freetronics/POEREG/Images/100_1713.JPG

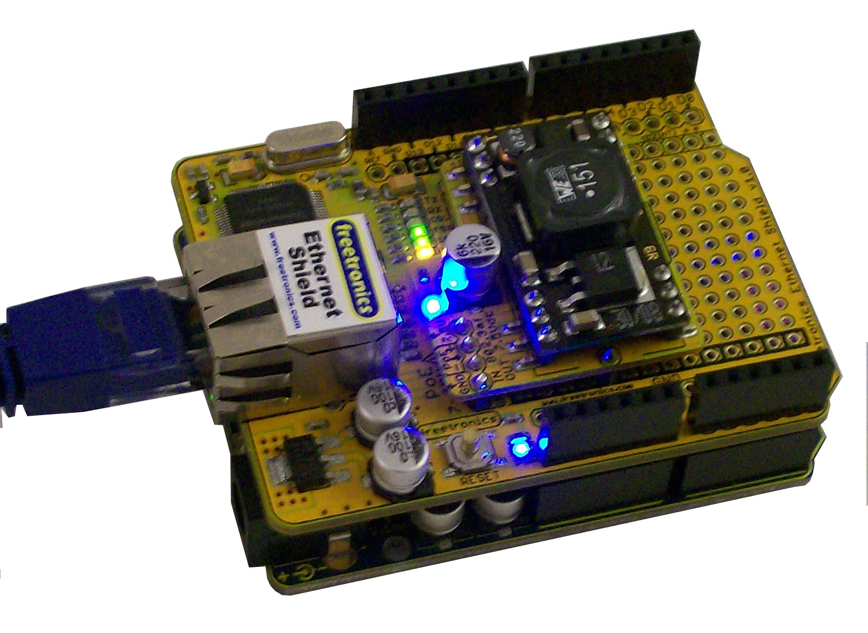
Images/100_1713.JPG
