freetronics/POEREG/Images/100_1719.JPG

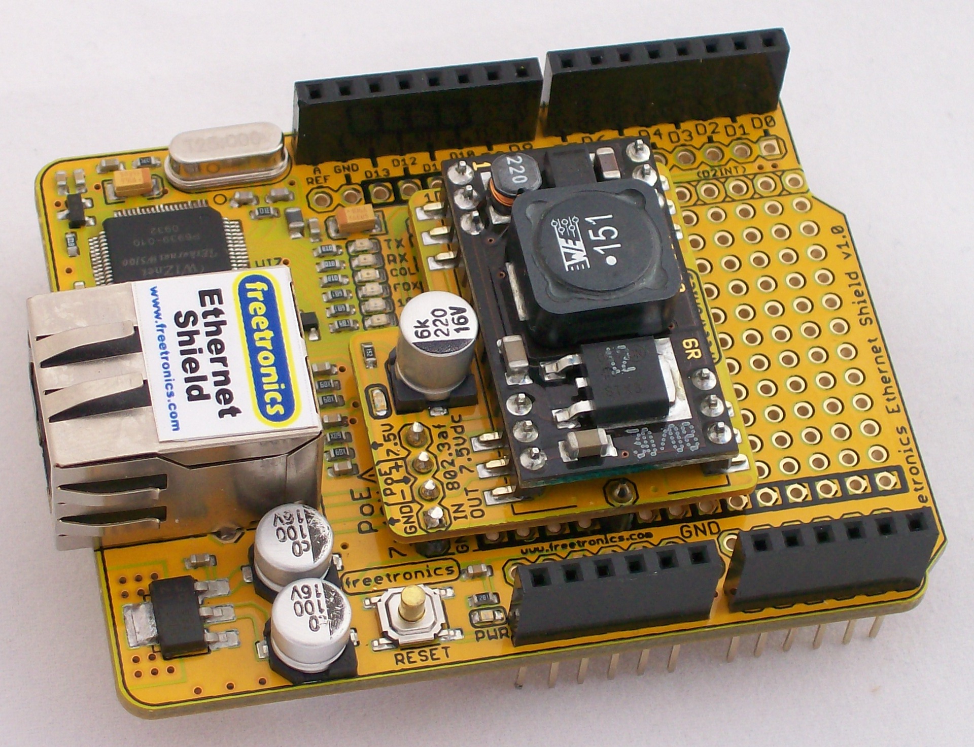
Images/100_1719.JPG
