freetronics/POEREG/Images/DSCF0289.JPG

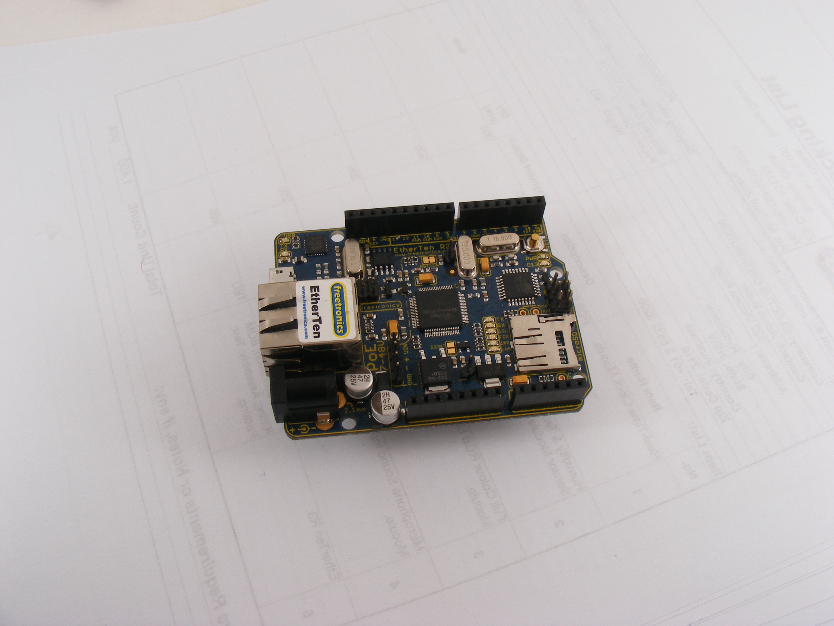
Images/DSCF0289.JPG
