freetronics/POEREG/Images/DSCF0290.JPG

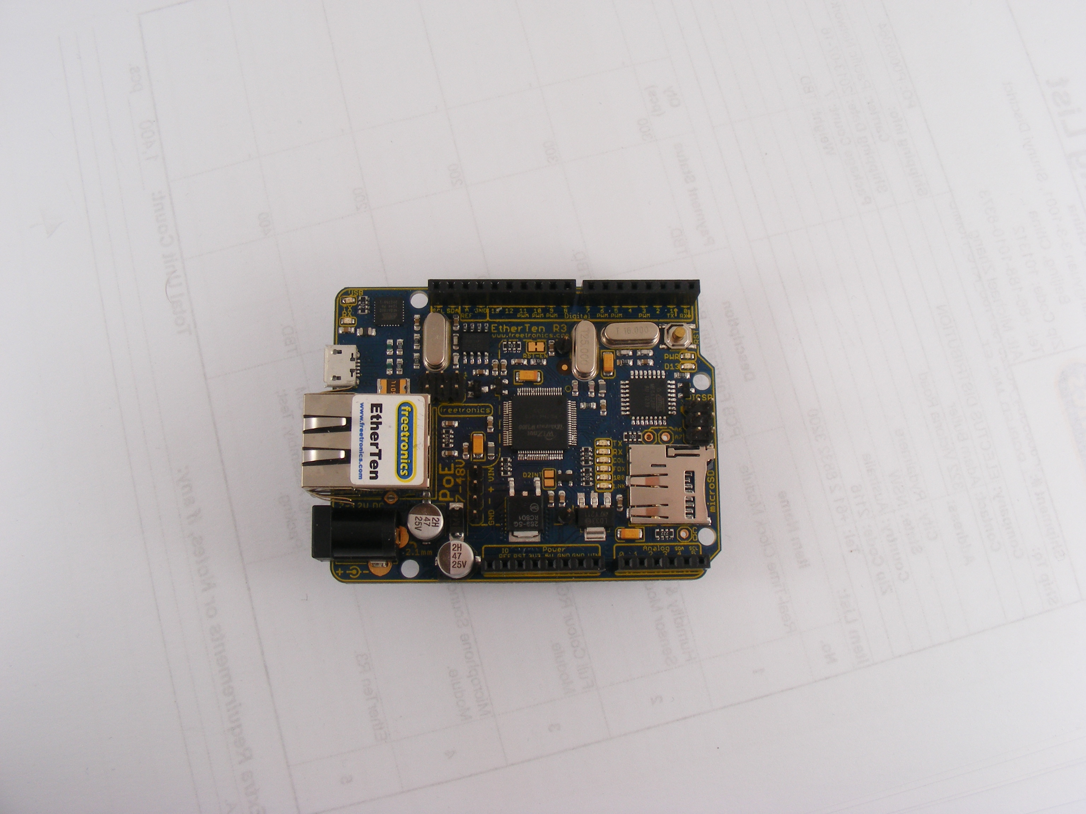
Images/DSCF0290.JPG
