freetronics/POEREG/Images/DSCF0296.JPG

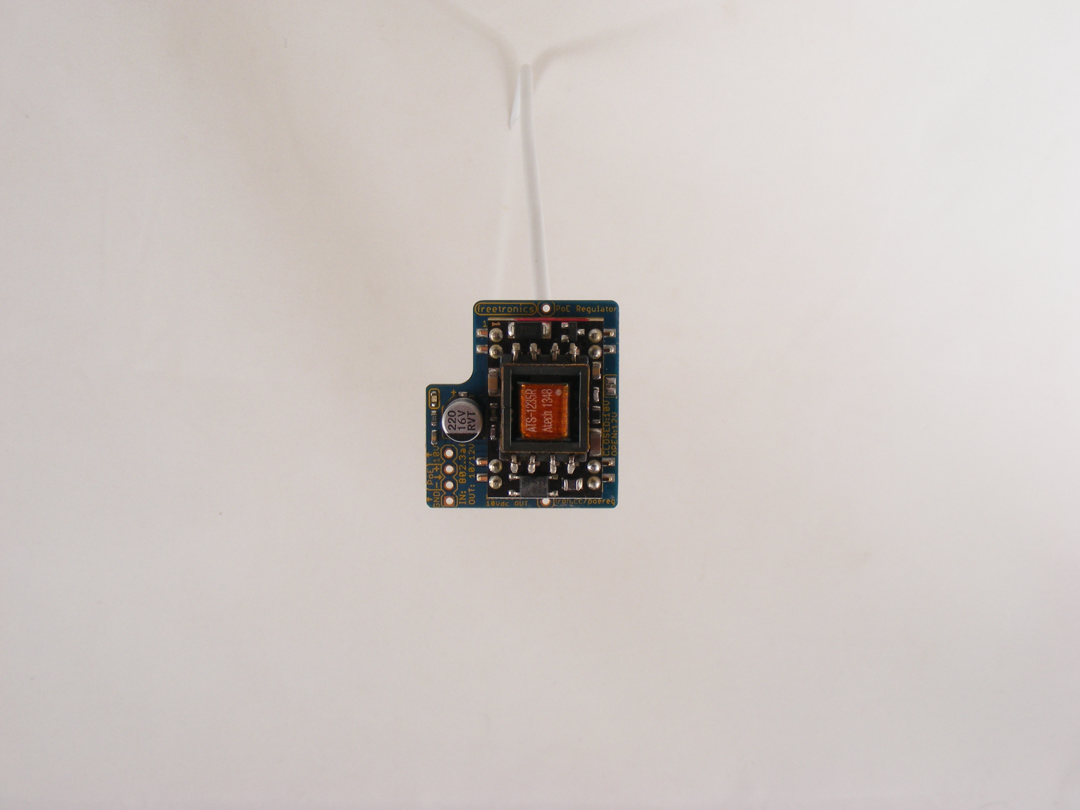
Images/DSCF0296.JPG
