freetronics/POEREG/Images/DSCF0299.JPG

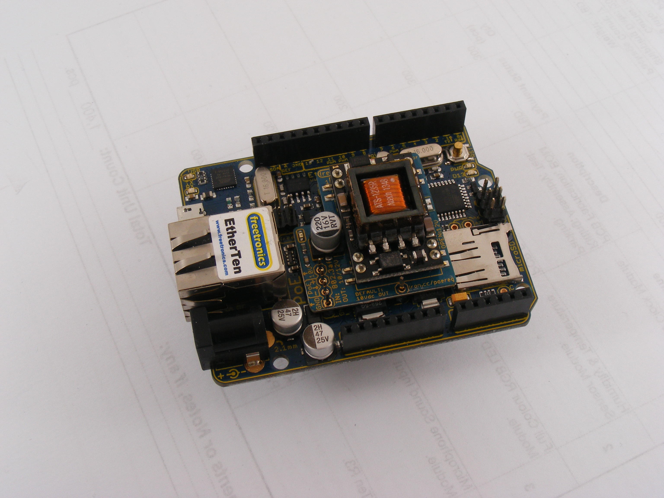
Images/DSCF0299.JPG
