freetronics/POEREG/Images/DSCF0301.JPG

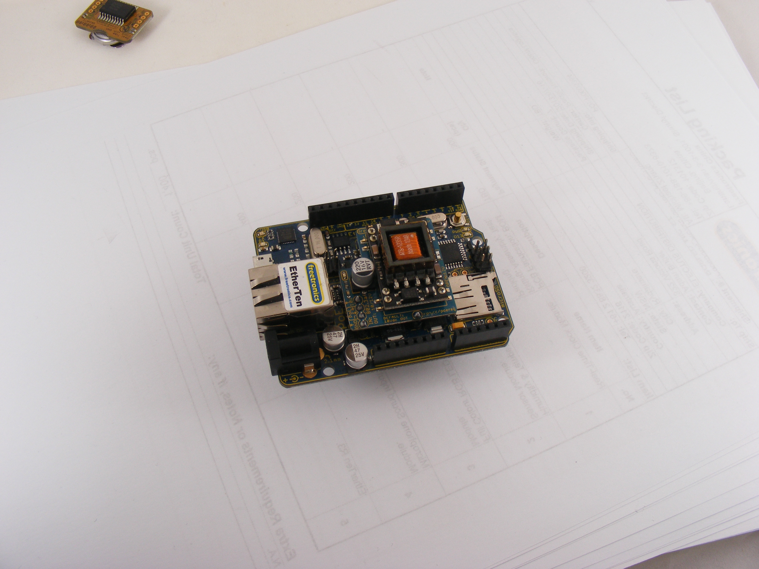
Images/DSCF0301.JPG
