freetronics/POEREG/Images/IMG_1117(4272x2848) (Custom).JPG

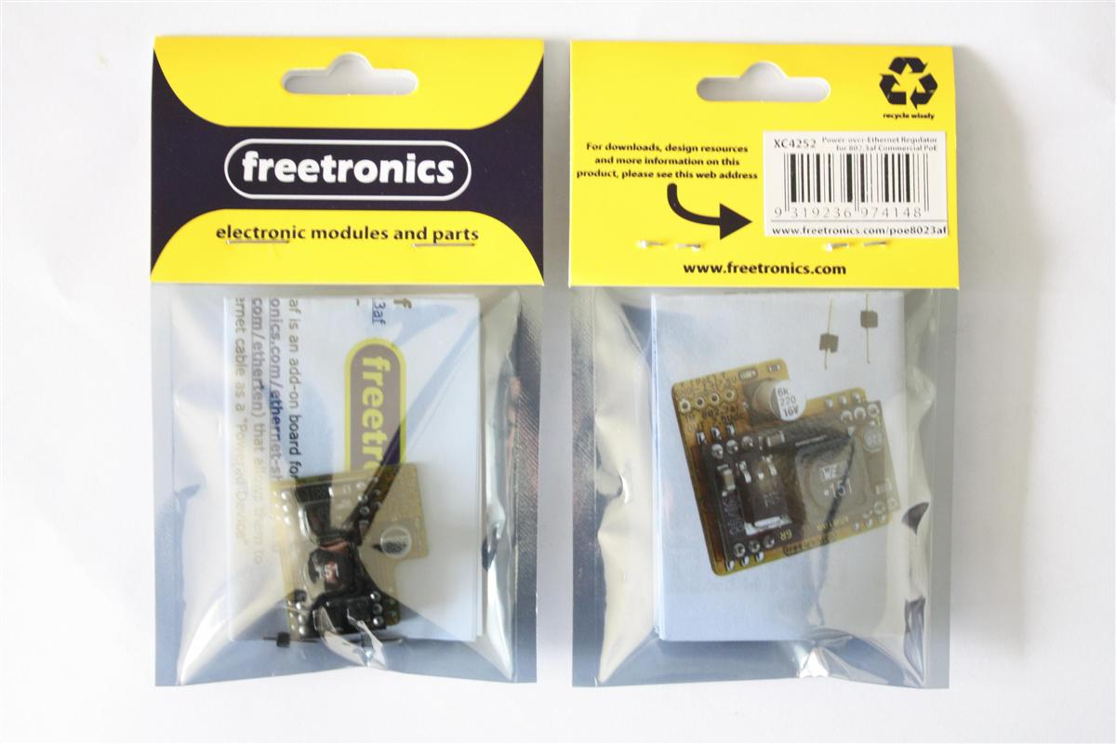
Images/IMG_1117(4272x2848) (Custom).JPG
