freetronics/POEREG/Images/reg8023-oblique-800.png

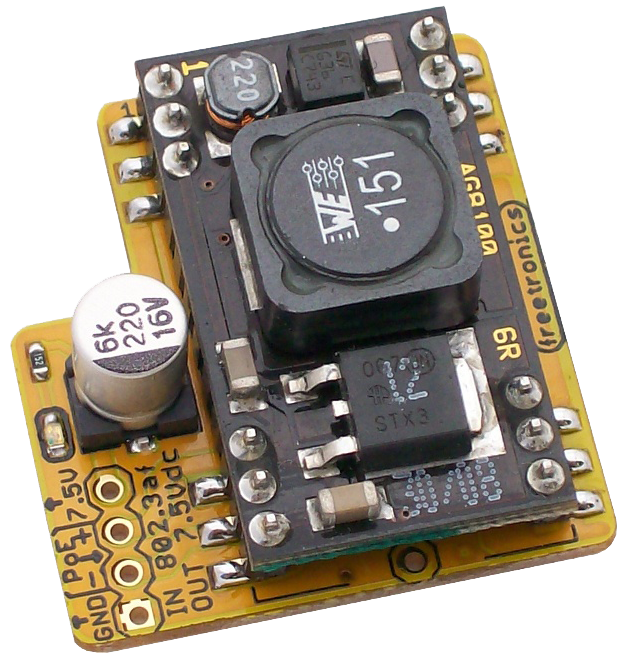
Images/reg8023-oblique-800.png
