freetronics/POEREG/Images/REG8023AF-v2_0-top.jpg

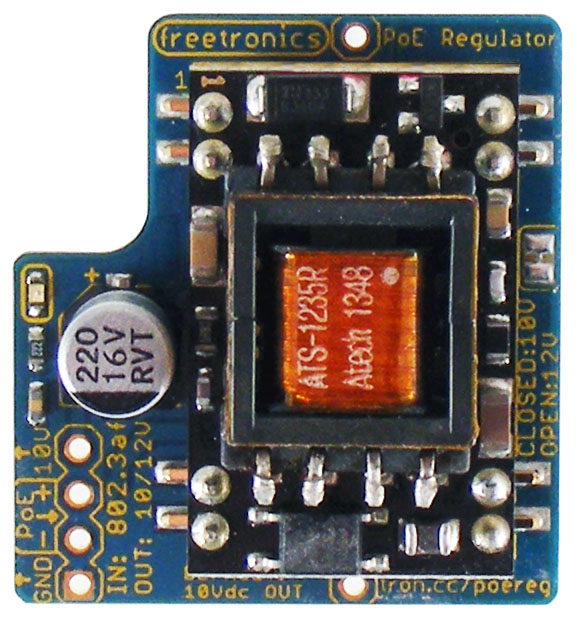
Images/REG8023AF-v2_0-top.jpg
