freetronics/POEREG/Packaging/2016-02-18 09.32.16.jpg

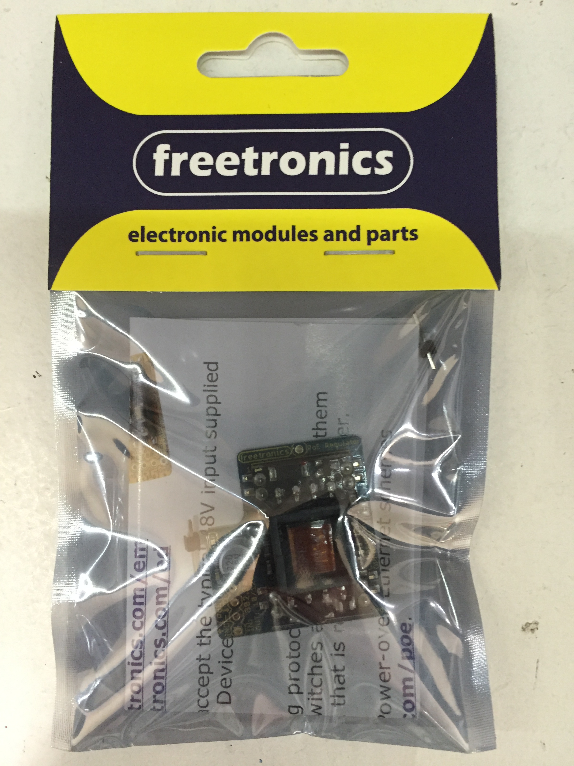
Packaging/2016-02-18 09.32.16.jpg
